dshadoff/PCE_ReDevelo/Software/python/develo.py

# Develo library for communication with the
# "ReDevelo" box and the PC Engine
#
import os
import serial

#
# Grab Develo's COM port from the environment variable
#
def get_portnum():
    if 'DEVELO_PORT' not in os.environ:
        sys.exit("DEVELO_PORT not defined")
    return os.environ.get('DEVELO_PORT')

#
# Open Develo's COM port
#
def open(comport):
    try:
        ser = serial.Serial(comport, 19200, timeout=1)
    except:
        print("Couldn't open serial port", comport)
        exit(1)
    return ser

#
# Close Develo's COM port
#
def close(port):
    port.close

#
# Just print out any response information from the
# serial port (used from debugging)
#
def pr_from_port(port):
    while 1:
        byte = port.read(1)
        print(byte.decode('utf-8'),end='',flush=True)
#        print(byte,end='',flush=True)

#
# Develo command to set a specific bank register
#   page = 0-7
#   bank = 0-255
#
def setbank(port, page, bank):
    port.write(b'A')
    port.write(page.to_bytes(1,'big'))
    port.write(bank.to_bytes(1,'big'))
    port.flush()
    ret = port.read(1)
    return ret

#
# Develo command to get all bank registers
#   returns a bytes object
#
def getbank(port):
    port.write(b'B')
    port.flush()
    ret = port.read(1);
    if ret == b'\x00':
        banks = port.read(8)
    else:
        banks = b'\x00'
    return ret, banks

#
# Develo command to get data from PC Engine main memory
#   returns a bytes object
#
#   addr     = 0-65536, PC Engine's memory address
#   numbytes = size of data to return
#
#  NOTE: Each remote fetch limited to 512 bytes
#
def getram_chunk(port, addr, numbytes):
    port.write(b'D')
    port.write(addr.to_bytes(2,'big'))
    port.write(numbytes.to_bytes(2,'big'))
    port.flush()
    ret = port.read(1);
    if ret == b'\x00':
        mem = port.read(numbytes)
    else:
        mem = b'\x00'
    return ret, mem

#
# Develo command to get data from PC Engine main memory
#   returns a bytes object
#
# Iterates getram_chunk() in 512-byte chunks until done
#   addr     = 0-65536, PC Engine's memory address
#   numbytes = size of data to return
#
def getram(port, addr, numbytes):
    assert numbytes != 0, "getram: numbytes should be non-zero"
    count = 0
    while numbytes > 0:
        chunksize = min(numbytes, 512)
        ret, mem = getram_chunk(port, addr, chunksize)
        if ret == b'\x00':
            if count == 0:
                allmem = mem
                count = count + 1
            else:
                allmem = allmem + mem
            addr = addr + chunksize
            numbytes = numbytes - chunksize
        else:
            allmem = b'\x00'
            break
    return ret, allmem

#
# Develo command to set memory
#   accepts a bytes object (and calculates size from it)
#
#   addr = 0-65536, PC Engine's memory address
#   mem  = data to load into PC Engine's memory
#
#  NOTE: Each remote fetch limited to 512 bytes
#
def setram_chunk(port, addr, mem):
    port.write(b'E')
    port.write(addr.to_bytes(2,'big'))
    size = len(mem)
    port.write(size.to_bytes(2,'big'))
    port.flush()
    port.write(mem)
    port.flush()
    ret = port.read(1)
    return ret

#
# Develo command to load data into PC Engine main memory
#   returns a bytes object
#
# Iterates setram_chunk() in 512-byte chunks until done
#   addr     = 0-65536, PC Engine's memory address
#   mem  = data to load into PC Engine's memory
#
def setram(port, addr, allmem):
    assert len(allmem) != 0, "setram: numbytes should be non-zero"
    start = 0
    end = len(allmem)
    numbytes = end - start
    while numbytes > 0:
        chunksize = min(numbytes, 512)
        mem = allmem[start:(start+chunksize)]
        ret = setram_chunk(port, addr, mem)
        if ret == b'\x00':
            start = start + chunksize
            addr = addr + chunksize
            numbytes = end - start
        else:
            break
    return ret


#
# Develo command to get data from PC Engine VRAM
#   returns a bytes object
#
#   addr     = 0-65536, PC Engine's VRAM address (*) but only 32768 addressable
#   numbytes = size of data to return
#
#  NOTE: Each remote fetch limited to 512 bytes
#
def getvram_chunk(port, addr, numbytes):
    port.write(b'F')
    port.write(addr.to_bytes(2,'big'))
    port.write(numbytes.to_bytes(2,'big'))
    port.flush()
    ret = port.read(1);
    if ret == b'\x00':
        mem = port.read(numbytes)
    else:
        mem = b'\x00'
    return ret, mem

#
# Develo command to get data from PC Engine VRAM
#   returns a bytes object
#
# Iterates getvram_chunk() in 512-byte chunks until done
#   addr     = 0-65536, PC Engine's VRAM address (*) but only 32768 addressable
#   numbytes = size of data to return
#
def getvram(port, addr, numbytes):
    assert numbytes != 0, "getvram: numbytes should be non-zero"
    count = 0
    while numbytes > 0:
        chunksize = min(numbytes, 512)
        ret, mem = getvram_chunk(port, addr, chunksize)
        if ret == b'\x00':
            if count == 0:
                allmem = mem
                count = count + 1
            else:
                allmem = allmem + mem
            addr = addr + int(chunksize / 2)
            numbytes = numbytes - chunksize
        else:
            allmem = b'\x00'
            break
    return ret, allmem

#
# Develo command to load data into VRAM
#   accepts a bytes object (and calculates size from it)
#
#   addr = 0-65536, PC Engine's VRAM address (*) but only 32768 addressable
#   mem  = data to load into PC Engine's VRAM
#
#  NOTE: Each remote fetch limited to 512 bytes
#
def setvram_chunk(port, addr, mem):
    port.write(b'G')
    port.write(addr.to_bytes(2,'big'))
    size = len(mem)
    port.write(size.to_bytes(2,'big'))
    port.flush()
    port.write(mem)
    port.flush()
    ret = port.read(1)
    return ret

#
# Develo command to load data into VRAM
#   accepts a bytes object (and calculates size from it)
#
# Iterates setvram_chunk() in 512-byte chunks until done
#   addr = 0-65536, PC Engine's VRAM address (*) but only 32768 addressable
#   mem  = data to load into PC Engine's VRAM
#
def setvram(port, addr, allmem):
    assert len(allmem) != 0, "setvram: numbytes should be non-zero"
    start = 0
    end = len(allmem)
    numbytes = end - start
    while numbytes > 0:
        chunksize = min(numbytes, 512)
        mem = allmem[start:(start+chunksize)]
        ret = setvram_chunk(port, addr, mem)
        if ret == b'\x00':
            start = start + chunksize
            addr = addr + int(chunksize/2)
            numbytes = end - start
        else:
            break
    return ret

#
# Develo command to get palette data
#   returns a bytes object
#
#   addr     = 0-511, PC Engine's palette address
#   numbytes = size of data to return
#
#  NOTE: Each remote fetch limited to 512 bytes
#
def getpal_chunk(port, addr, numbytes):
    port.write(b'H')
    port.write(addr.to_bytes(2,'big'))
    port.write(numbytes.to_bytes(2,'big'))
    port.flush()
    ret = port.read(1);
    if ret == b'\x00':
        mem = port.read(numbytes)
    else:
        mem = b'\x00'
    return ret, mem

#
# Develo command to get palette data
#   returns a bytes object
#
# Iterates getpal_chunk() in 512-byte chunks until done
#   addr     = 0-511, PC Engine's palette address
#   numbytes = size of data to return
#
def getpal(port, addr, numbytes):
    assert numbytes != 0, "getpal: numbytes should be non-zero"
    count = 0
    while numbytes > 0:
        chunksize = min(numbytes, 512)
        ret, mem = getpal_chunk(port, addr, chunksize)
        if ret == b'\x00':
            if count == 0:
                allmem = mem
                count = count + 1
            else:
                allmem = allmem + mem
            addr = addr + int(chunksize / 2)
            numbytes = numbytes - chunksize
        else:
            allmem = b'\x00'
            break
    return ret, allmem

#
# Develo command to load data into palettes
#   accepts a bytes object (and calculates size from it)
#
#   addr = 0-511, PC Engine's palette address
#   mem  = data to load into palettes
#
#  NOTE: Each remote fetch limited to 512 bytes
#
def setpal_chunk(port, addr, mem):
    port.write(b'I')
    port.write(addr.to_bytes(2,'big'))
    size = len(mem)
    port.write(size.to_bytes(2,'big'))
    port.flush()
    port.write(mem)
    port.flush()
    ret = port.read(1)
    return ret

#
# Develo command to load data into palettes
#   accepts a bytes object (and calculates size from it)
#
# Iterates setpal_chunk() in 512-byte chunks until done
#   addr = 0-511, PC Engine's palette address
#   mem  = data to load into PC Engine's VRAM
#
def setpal(port, addr, allmem):
    assert len(allmem) != 0, "setpal: numbytes should be non-zero"
    start = 0
    end = len(allmem)
    numbytes = end - start
    while numbytes > 0:
        chunksize = min(numbytes, 512)
        mem = allmem[start:(start+chunksize)]
        ret = setpal_chunk(port, addr, mem)
        if ret == b'\x00':
            start = start + chunksize
            addr = addr + int(chunksize/2)
            numbytes = end - start
        else:
            break
    return ret

#
# Develo command to execute at a location
#
#   addr = memory location to execute at
#
def exec(port, addr):
    port.write(b'J')
    port.write(addr.to_bytes(2,'big'))
    port.flush()
    ret = port.read(1)
    return ret

#
# Develo command to reed CD sector data
#   returns a bytes object
#
#   addr = 0-0xffffff, PC Engine's sector address, relative to start of data track
#
# Note: As CD seek time is slow, there is an inserted delay before returning data
#
def getsector(port, addr):
    port.write(b'L')
    port.write(addr.to_bytes(3,'big'))
    port.flush()
    while port.in_waiting == 0:
        continue
    ret = port.read(1);
    if ret == b'\x00':
        mem = port.read(2048)
    else:
        mem = b'\x00'
    return ret, mem

#
# Develo test command to return an error code
# (not part of original system)
#    returns a return code
#
def err(port):
    port.write(b'Z')
    port.flush()
    ret = port.read(1);
    return ret

#
# Evaluate return code from develo command
# and print corresponding error message
#
def chkret(ret, text):
    if ret != b'\x00':
        print("Develo error",end=' ')
        print('{0:0{1}X}'.format(ret[0],2),end=' ')
        print("in",end=' ')
        print(text,end='. Terminating.')
        print()
        exit(1)
