dshadoff/PCE_ReDevelo/Firmware/Arduino/ReDevelo_MCU_sketch/define.h

//
// define.h
//
// Common Definitions file used by everybody
//
// (c) 2019, 2020, 2022 by David Shadoff


// names of keys
// Note that any multi-code key has special code defined here
//
// single-code keystrokes:
#define KEY_BACKSPACE    0x08
#define KEY_TAB          0x09
#define KEY_ENTER        0x0A
#define KEY_ESCAPE       0x1B
#define KEY_DELETE       0x7F
